vineethjkatti-tech/ATTN_unit/Assets/PCB/front_view.png

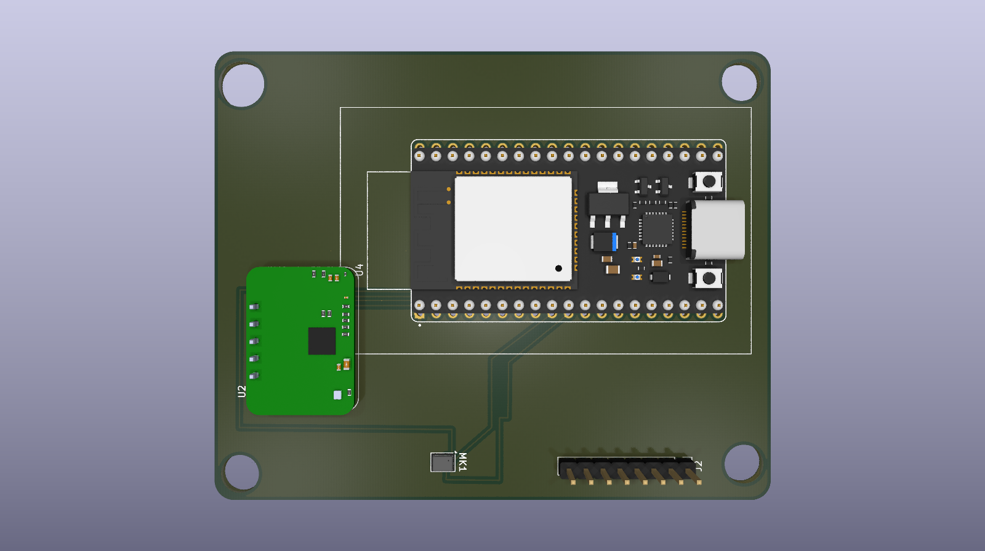
Assets/PCB/front_view.png
