vineethjkatti-tech/ATTN_unit/Assets/PCB/hero_shot.png

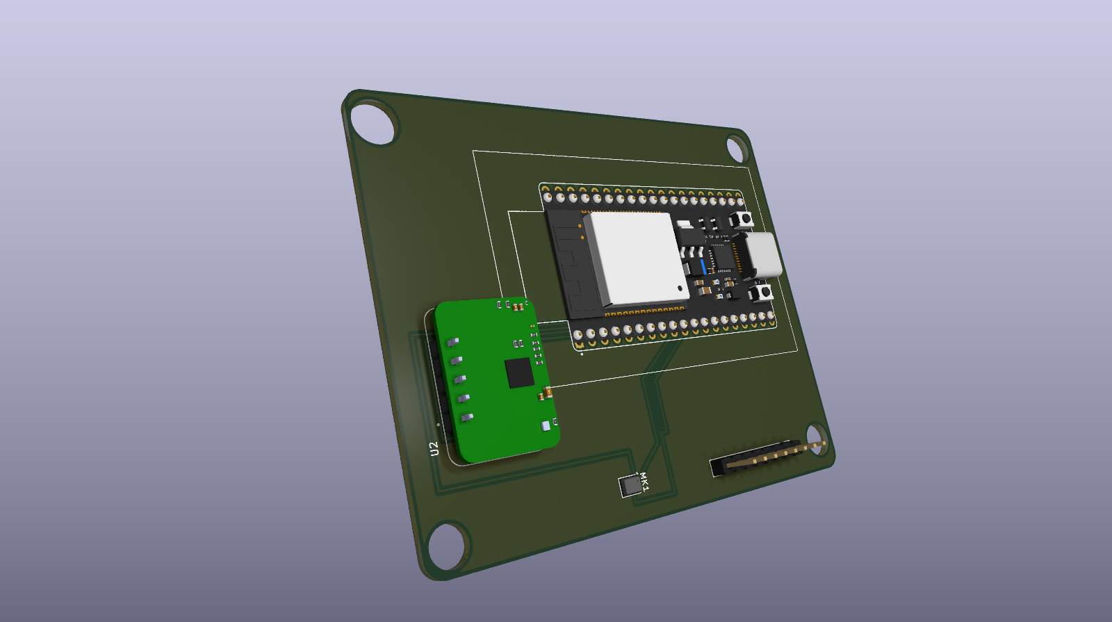
Assets/PCB/hero_shot.png
