vineethjkatti-tech/ATTN_unit/Assets/PCB/side_view.png

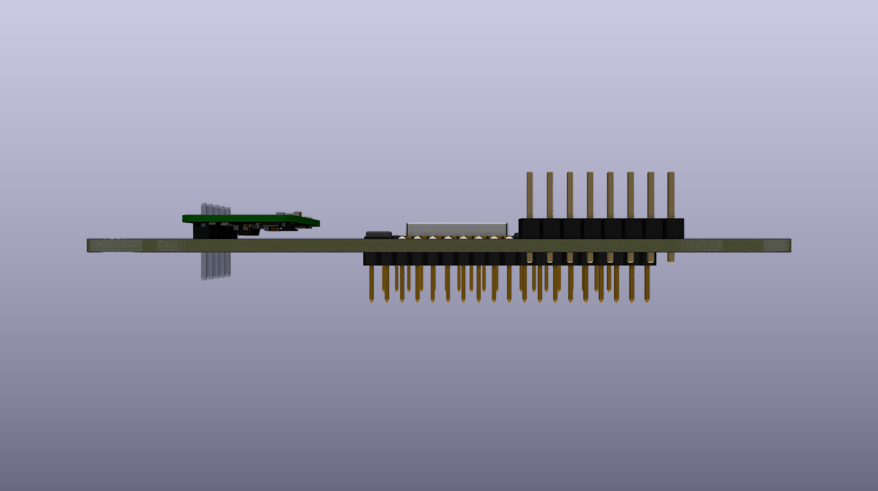
Assets/PCB/side_view.png
