vineethjkatti-tech/ATTN_unit/Assets/Assembly/front_view.png

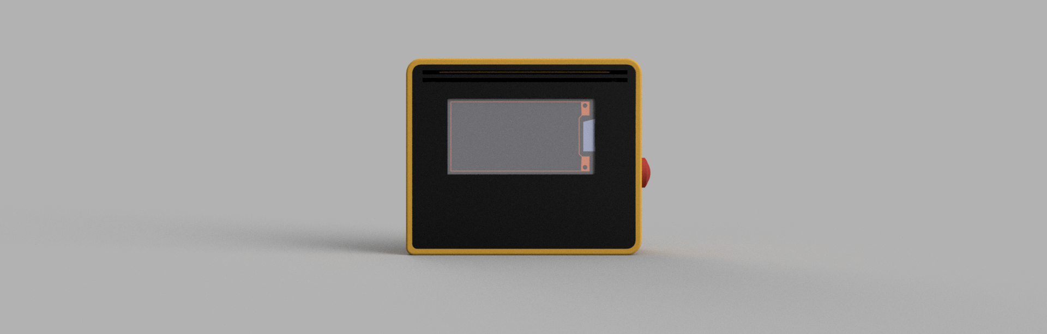
Assets/Assembly/front_view.png
