vineethjkatti-tech/ATTN_unit/journal/journal-images/Screenshot 2026-06-27 105707.png

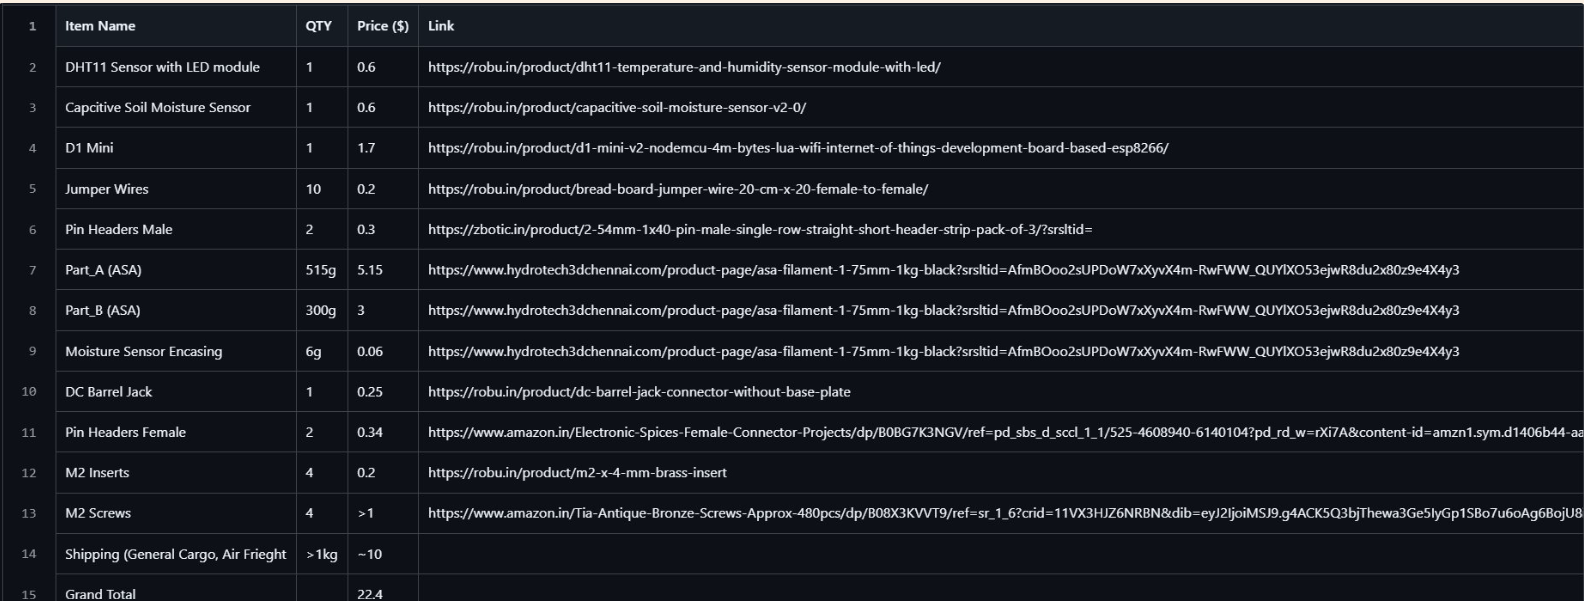
journal/journal-images/Screenshot 2026-06-27 105707.png
